perna5pr/PTT-PLUS/hardware/PTT_PLUS_1bt/PCB_PTT_PLUS_1bt_2026-09-06_tras.png

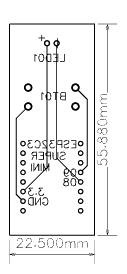
hardware/PTT_PLUS_1bt/PCB_PTT_PLUS_1bt_2026-09-06_tras.png
