perna5pr/PTT-PLUS/hardware/PTT_PLUS_1bt/PTT_PLUS_1bt_frente.png

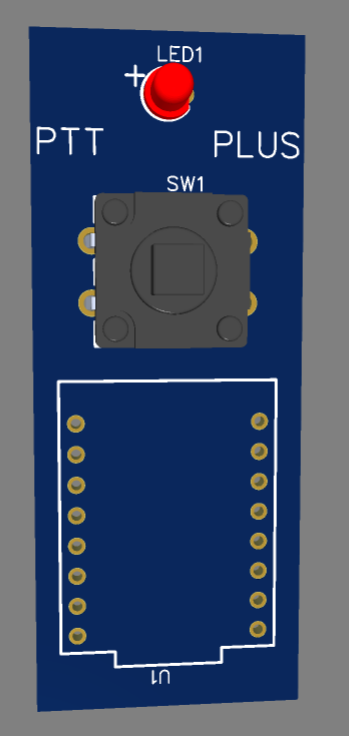
hardware/PTT_PLUS_1bt/PTT_PLUS_1bt_frente.png
