perna5pr/PTT-PLUS/hardware/PTT_PLUS_2bt/PCB_PTT_PLUS_2bt_3D_tras.png

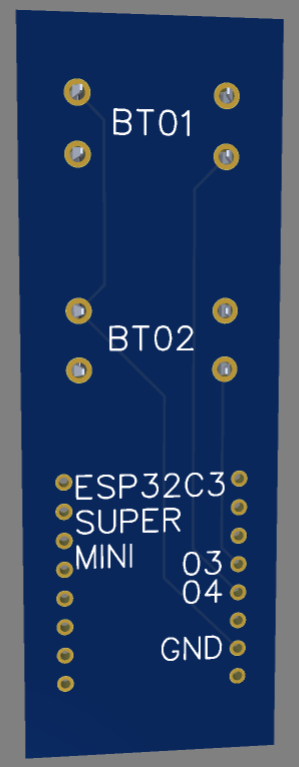
hardware/PTT_PLUS_2bt/PCB_PTT_PLUS_2bt_3D_tras.png
