perna5pr/PTT-PLUS/hardware/PTT_PLUS_2bt/PCB_PTT_PLUS_2bt_2026-09-06_tras.png

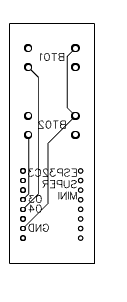
hardware/PTT_PLUS_2bt/PCB_PTT_PLUS_2bt_2026-09-06_tras.png
