perna5pr/PTT-PLUS/hardware/PTT_PLUS_2bt/ptt-2bt.jpeg

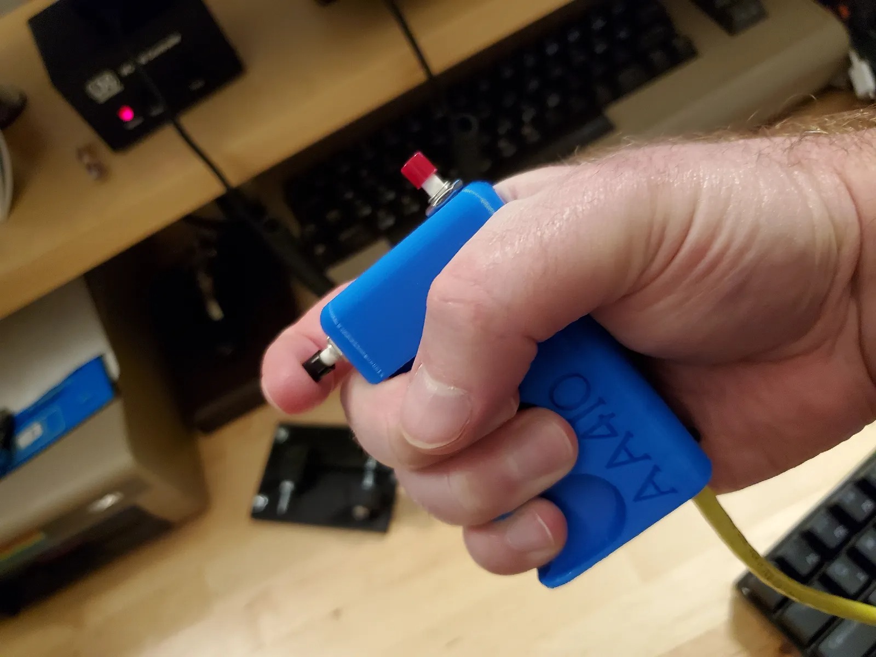
hardware/PTT_PLUS_2bt/ptt-2bt.jpeg
