perna5pr/PTT-PLUS/hardware/PTT_PLUS_4bt/PCB_PTT_PLUS_4bt_3D_tras.png

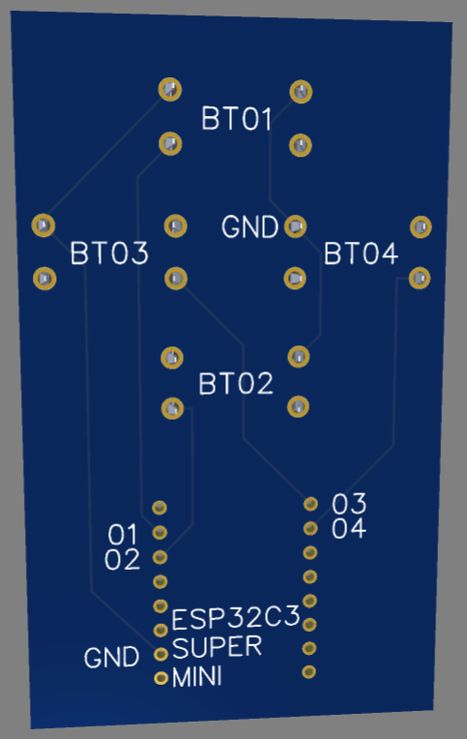
hardware/PTT_PLUS_4bt/PCB_PTT_PLUS_4bt_3D_tras.png
