perna5pr/PTT-PLUS/hardware/PTT_PLUS_4bt/PCB_PTT_PLUS_4bt_2026-09-06_frente.png

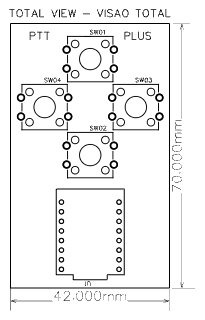
hardware/PTT_PLUS_4bt/PCB_PTT_PLUS_4bt_2026-09-06_frente.png
