perna5pr/PTT-PLUS/hardware/PTT_PLUS_4bt_oled/PCB_PTT_PLUS_4bt_oled_3D_tras.png

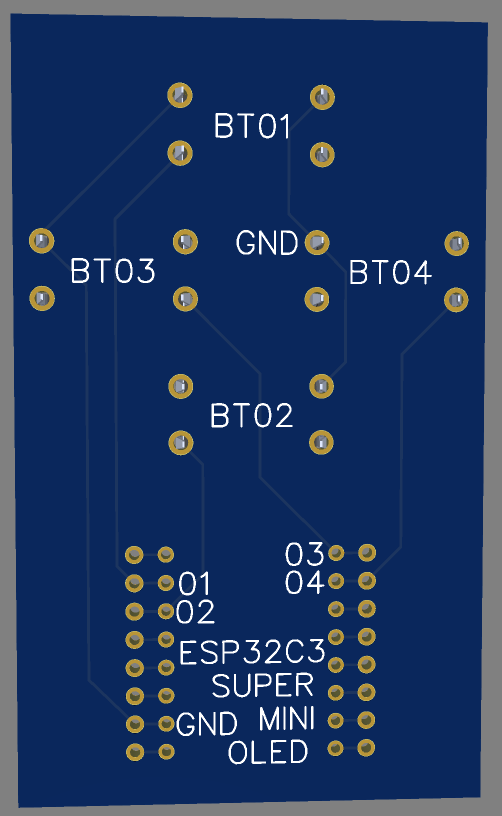
hardware/PTT_PLUS_4bt_oled/PCB_PTT_PLUS_4bt_oled_3D_tras.png
